JagdtigerAusfb/Rubiks_Cube_Solving_Robot_EXTENCUBE_UNICAMP/1. RAIDEN/3D Files/Cap_garra_v3.png

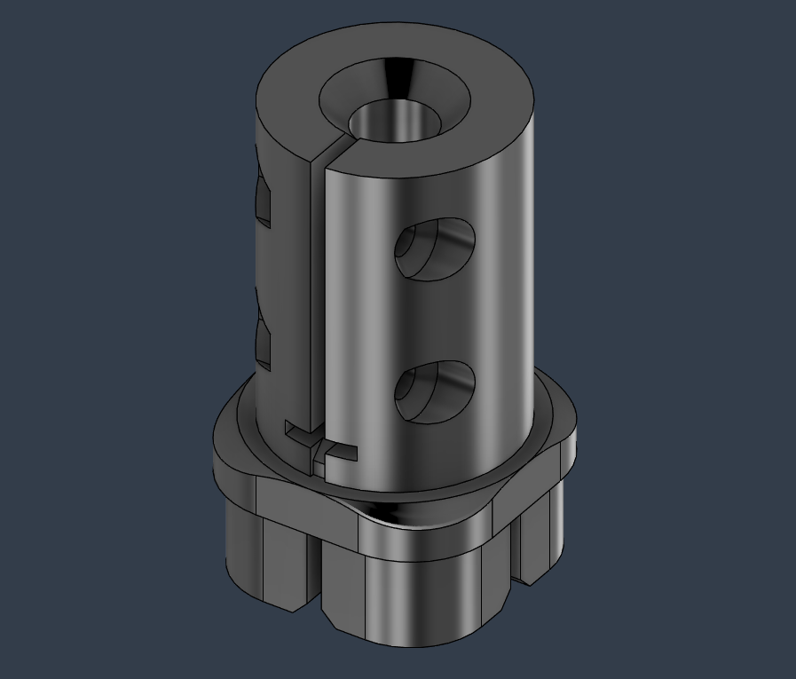
1. RAIDEN/3D Files/Cap_garra_v3.png
