JagdtigerAusfb/Rubiks_Cube_Solving_Robot_EXTENCUBE_UNICAMP/1. RAIDEN/3D Files/Gabarito_Final.png

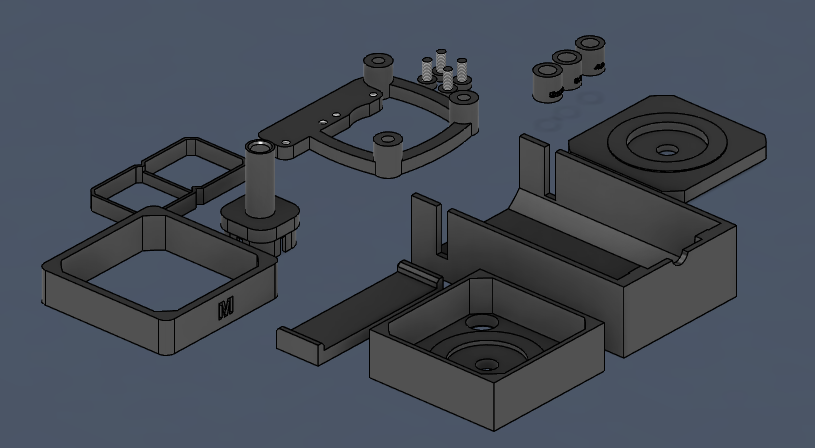
1. RAIDEN/3D Files/Gabarito_Final.png
