JagdtigerAusfb/Rubiks_Cube_Solving_Robot_EXTENCUBE_UNICAMP/1. RAIDEN/PCB/PCB 3 Drivers/3DriversA4988.png

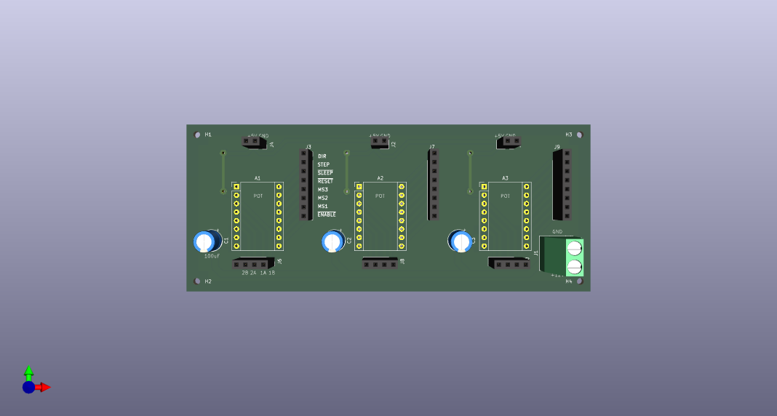
1. RAIDEN/PCB/PCB 3 Drivers/3DriversA4988.png
