JagdtigerAusfb/Rubiks_Cube_Solving_Robot_EXTENCUBE_UNICAMP/1. RAIDEN/PCB/PCB Drivers + Sensores/PCB Drivers + Sensores/PCB Drivers + Sensores.png

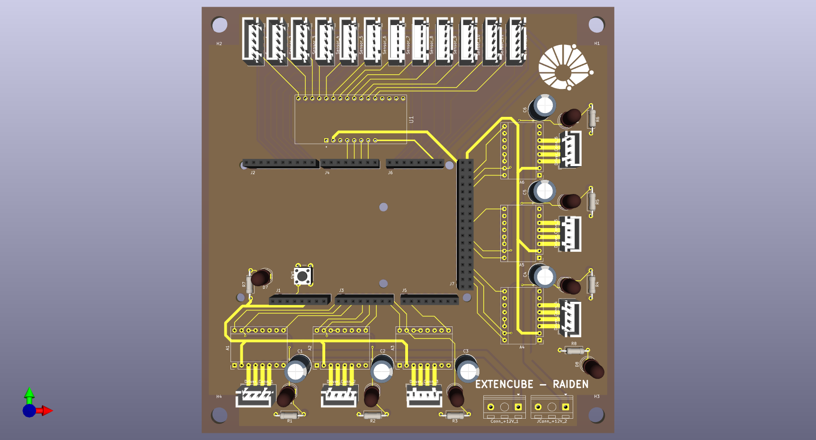
1. RAIDEN/PCB/PCB Drivers + Sensores/PCB Drivers + Sensores/PCB Drivers + Sensores.png
