JagdtigerAusfb/Rubiks_Cube_Solving_Robot_EXTENCUBE_UNICAMP/3. Códigos de Teste ou Demonstração/Sensores/Códigos Gerais/BETA/Calibração_V3_BETA.docx

#include <Wire.h>

#include <string.h>

/* Estrutura da Calibração

Esse código implementa a estrutura do

fluxograma da Calibração Completa do

Sistema dos Sensores.

*/

void ini_calib() {

// Inicializa Variáveis

int face, position, estado = 0, 0, 0;

int progression[6] = {0};

float calibration[12][6] = {-1};

// Define Constantes de Operação do Sistema

//Inserir aqui Parametros peso de HSV

int ordem[6][6] = {

{0, 1, 3, 4, 5, 2},

{1, 5, 4, 2, 0, 3},

{2, 1, 5, 4, 0, 3},

{3, 1, 0, 4, 2, 5},

{4, 2, 1, 5, 3, 0},

{5, 4, 2, 1, 3, 0}

};

int seq_faces[] = {

0,3, 0,3, 0,3, 0,3,

2,1,5,4, 2,1,5,4, 2,1,5,4, 2,1,5,4,

0,3, 0,3,

2,5, 2,5,

1,4, 1,4

};

char seq_moves[][7] = {

"PG", "PG", "PG", "PG",

"A", "A", "A",

"AEBK", "JAFBK",

"JAFHP", "GQFHP",

"GQEQEM", "DNREM",

"DNQ"

};

bool flags_move[] = {

0,0,1,0,1,0,1,0,

1,0,0,0, 1,0,0,0, 1,0,0,0, 1,0,0,0,

1,0,1,0,

1,0,1,0,

1,0,1,0,

1

};

}

void setup() {

Serial.begin(115200);

Wire.begin();

ini_calib();

}

void sens_calib() {

int NS = 2*face + position;

// Ler RGB Sensor NS (precisa acionar portas especificas, fazer com switch case)

// Converter RGB para HSV

float H_medido = 0.0; //exemplo

int b = progression[face];

int indice = ordem[face][b];

calibration[NS][indice] = H_medido;

estado++;

}

void loop_calibration() {

while(1) {

sens_calib();

if (position == 0){

position = 1;

continue;

}

position = 0;

progression[face]++;

if (estado == 72) {

//Faz Etapas Finais para encerrrar Calibração

break;

}

int a = estado>>1;

face = seq_faces[a];

if (flags_move[a]) {

char move[7];

strcpy(move, seq_moves[a]);

// Executar move da string pega acima

}

}

}

void loop() {

loop_calibration();

}
