JagdtigerAusfb/Rubiks_Cube_Solving_Robot_EXTENCUBE_UNICAMP/3. Códigos de Teste ou Demonstração/Sensores/Códigos Gerais/BETA/Calibração_V4_BETA_MONOBLOCO.docx

#include <Wire.h>

#include <string.h>

#include "TCS34725.h"

/* Estrutura da Calibração

Esse código implementa a estrutura do

fluxograma da Calibração Completa do

Sistema dos Sensores.

*/

TCS34725 tcs;

#define AMOSTRAS 20

int NS;

bool ini_calib;

// MULTIPLEXADOR

#define LED_0 0

#define LED_1 1

#define LED_2 2

#define LED_3 3

#define LED_4 4

#define LED_5 5

#define LED_6 6

#define LED_7 7

#define LED_8 8

#define LED_9 9

#define LED_10 10

#define LED_11 11

#define EN_MUX 18

#define MUX_0 17

#define MUX_1 16

#define MUX_2 15

#define MUX_3 14

//

//PARTE DOS MOTORES

#define DIR_PIN_1 31

#define STEP_PIN_1 30

#define DIR_PIN_2 35

#define STEP_PIN_2 34

#define DIR_PIN_3 A12

#define STEP_PIN_3 A13

#define DIR_PIN_4 A6

#define STEP_PIN_4 A7

#define DIR_PIN_5 A0

#define STEP_PIN_5 A1

#define DIR_PIN_6 43

#define STEP_PIN_6 42

#define ENABLE_PIN_1 14

#define ENABLE_PIN_2 16

#define ENABLE_PIN_3 49

#define ENABLE_PIN_4 48

#define ENABLE_PIN_5 A3

#define ENABLE_PIN_6 19

// ================================

// CONFIG

// ================================

#define MAX_SEQ 350

char lineBuffer[50];

char sequencia[MAX_SEQ];

int seqLen = 0;

int DELAY_STEP = 1000;

int DELAY_ENTRE_MOV = 10;

bool recebendo = false;

// ================================

// CONFIGURAR MOTOR

// ================================

bool configurarMotor(char m, int &dirPin, int &stepPin, int &enablePin, int &dir, int &passos) {

switch(m) {

case 'A': dirPin=DIR_PIN_1; stepPin=STEP_PIN_1; enablePin=ENABLE_PIN_1; dir=LOW; passos=50; break;

case 'B': dirPin=DIR_PIN_1; stepPin=STEP_PIN_1; enablePin=ENABLE_PIN_1; dir=HIGH; passos=50; break;

case 'C': dirPin=DIR_PIN_1; stepPin=STEP_PIN_1; enablePin=ENABLE_PIN_1; dir=LOW; passos=100; break;

case 'D': dirPin=DIR_PIN_2; stepPin=STEP_PIN_2; enablePin=ENABLE_PIN_2; dir=LOW; passos=50; break;

case 'E': dirPin=DIR_PIN_2; stepPin=STEP_PIN_2; enablePin=ENABLE_PIN_2; dir=HIGH; passos=50; break;

case 'F': dirPin=DIR_PIN_2; stepPin=STEP_PIN_2; enablePin=ENABLE_PIN_2; dir=LOW; passos=100; break;

case 'G': dirPin=DIR_PIN_3; stepPin=STEP_PIN_3; enablePin=ENABLE_PIN_3; dir=LOW; passos=50; break;

case 'H': dirPin=DIR_PIN_3; stepPin=STEP_PIN_3; enablePin=ENABLE_PIN_3; dir=HIGH; passos=50; break;

case 'I': dirPin=DIR_PIN_3; stepPin=STEP_PIN_3; enablePin=ENABLE_PIN_3; dir=LOW; passos=100; break;

case 'J': dirPin=DIR_PIN_4; stepPin=STEP_PIN_4; enablePin=ENABLE_PIN_4; dir=LOW; passos=50; break;

case 'K': dirPin=DIR_PIN_4; stepPin=STEP_PIN_4; enablePin=ENABLE_PIN_4; dir=HIGH; passos=50; break;

case 'L': dirPin=DIR_PIN_4; stepPin=STEP_PIN_4; enablePin=ENABLE_PIN_4; dir=LOW; passos=100; break;

case 'M': dirPin=DIR_PIN_5; stepPin=STEP_PIN_5; enablePin=ENABLE_PIN_5; dir=LOW; passos=50; break;

case 'N': dirPin=DIR_PIN_5; stepPin=STEP_PIN_5; enablePin=ENABLE_PIN_5; dir=HIGH; passos=50; break;

case 'O': dirPin=DIR_PIN_5; stepPin=STEP_PIN_5; enablePin=ENABLE_PIN_5; dir=LOW; passos=100; break;

case 'P': dirPin=DIR_PIN_6; stepPin=STEP_PIN_6; enablePin=ENABLE_PIN_6; dir=LOW; passos=50; break;

case 'Q': dirPin=DIR_PIN_6; stepPin=STEP_PIN_6; enablePin=ENABLE_PIN_6; dir=HIGH; passos=50; break;

case 'R': dirPin=DIR_PIN_6; stepPin=STEP_PIN_6; enablePin=ENABLE_PIN_6; dir=LOW; passos=100; break;

default: return false;

}

return true;

}

// ================================

// EXECUÇÕES

// ================================

void executarSimples(char m){

int d,s,e,dir,p;

if(!configurarMotor(m,d,s,e,dir,p)) return;

digitalWrite(e,LOW);

digitalWrite(d,dir);

for(int i=0;i<p;i++){

digitalWrite(s,HIGH);

delayMicroseconds(DELAY_STEP);

digitalWrite(s,LOW);

delayMicroseconds(DELAY_STEP);

}

digitalWrite(e,HIGH);

delay(DELAY_ENTRE_MOV);

}

//

void setup() {

Serial.begin(115200);

Wire.begin();

tcs.integrationTime(33);

tcs.gain(TCS34725::Gain::X01);

ini_calib = true;

//Sensor

pinMode(LED_0, OUTPUT);

pinMode(LED_1, OUTPUT);

pinMode(LED_2, OUTPUT);

pinMode(LED_3, OUTPUT);

pinMode(LED_4, OUTPUT);

pinMode(LED_5, OUTPUT);

pinMode(LED_6, OUTPUT);

pinMode(LED_7, OUTPUT);

pinMode(LED_8, OUTPUT);

pinMode(LED_9, OUTPUT);

pinMode(LED_10, OUTPUT);

pinMode(LED_11, OUTPUT);

pinMode(EN_MUX, OUTPUT);

pinMode(MUX_0, OUTPUT);

pinMode(MUX_1, OUTPUT);

pinMode(MUX_2, OUTPUT);

pinMode(MUX_3, OUTPUT);

//Motor

pinMode(ENABLE_PIN_1,OUTPUT); digitalWrite(ENABLE_PIN_1,HIGH);

pinMode(ENABLE_PIN_2,OUTPUT); digitalWrite(ENABLE_PIN_2,HIGH);

pinMode(ENABLE_PIN_3,OUTPUT); digitalWrite(ENABLE_PIN_3,HIGH);

pinMode(ENABLE_PIN_4,OUTPUT); digitalWrite(ENABLE_PIN_4,HIGH);

pinMode(ENABLE_PIN_5,OUTPUT); digitalWrite(ENABLE_PIN_5,HIGH);

pinMode(ENABLE_PIN_6,OUTPUT); digitalWrite(ENABLE_PIN_6,HIGH);

pinMode(DIR_PIN_1,OUTPUT); pinMode(STEP_PIN_1,OUTPUT);

pinMode(DIR_PIN_2,OUTPUT); pinMode(STEP_PIN_2,OUTPUT);

pinMode(DIR_PIN_3,OUTPUT); pinMode(STEP_PIN_3,OUTPUT);

pinMode(DIR_PIN_4,OUTPUT); pinMode(STEP_PIN_4,OUTPUT);

pinMode(DIR_PIN_5,OUTPUT); pinMode(STEP_PIN_5,OUTPUT);

pinMode(DIR_PIN_6,OUTPUT); pinMode(STEP_PIN_6,OUTPUT);

}

void rgbToHsv(float r, float g, float b, float &h, float &s, float &v) {

float maxc = max(r, max(g, b));

float minc = min(r, min(g, b));

float delta = maxc - minc;

v = maxc;

if (maxc == 0) { s = 0; h = 0; return; }

s = delta / maxc;

if (delta == 0) h = 0;

else if (maxc == r) h = 60.0 * fmod(((g - b) / delta), 6);

else if (maxc == g) h = 60.0 * (((b - r) / delta) + 2);

else h = 60.0 * (((r - g) / delta) + 4);

if (h < 0) h += 360.0;

}

float sensor() {

if (!tcs.attach(Wire)) {

Serial.print("Sensor ");

Serial.print(NS);

Serial.println(" nao encontrado!");

// Aguarda Sensor conectar

while (1);

}

delay(4000); // alterar delay?

int validas = 0;

float H_mean = -1;

float somaHue = 0;

for (int i = 0; i < AMOSTRAS; i++) {

while (!tcs.available());

auto c = tcs.color();

float r = c.r, g = c.g, b = c.b;

float soma = r + g + b;

if (soma < 5) continue;

r /= soma;

g /= soma;

b /= soma;

float h, s, v;

rgbToHsv(r, g, b, h, s, v);

somaHue += h;

validas++;

if (validas > 0) {H_mean = somaHue / validas;}

delay(50);

return(H_mean);

}

}

void MUX(int n){

digitalWrite(EN_MUX, LOW);

digitalWrite(LED_0, LOW);

digitalWrite(LED_1, LOW);

digitalWrite(LED_2, LOW);

digitalWrite(LED_3, LOW);

digitalWrite(LED_4, LOW);

digitalWrite(LED_5, LOW);

digitalWrite(LED_6, LOW);

digitalWrite(LED_7, LOW);

digitalWrite(LED_8, LOW);

digitalWrite(LED_9, LOW);

digitalWrite(LED_10, LOW);

digitalWrite(LED_11, LOW);

switch(n) {

case 1:

digitalWrite(LED_1, HIGH);

break;

case 2:

digitalWrite(LED_2, HIGH);

break;

case 3:

digitalWrite(LED_3, HIGH);

break;

case 4:

digitalWrite(LED_4, HIGH);

break;

case 5:

digitalWrite(LED_5, HIGH);

break;

case 6:

digitalWrite(LED_6, HIGH);

break;

case 7:

digitalWrite(LED_7, HIGH);

break;

case 8:

digitalWrite(LED_8, HIGH);

break;

case 9:

digitalWrite(LED_9, HIGH);

break;

case 10:

digitalWrite(LED_10, HIGH);

break;

case 11:

digitalWrite(LED_11, HIGH);

break;

default:

digitalWrite(LED_0, HIGH);

} // Liga o LED do sensor NS

if (NS & 1<<0) {digitalWrite(MUX_0, HIGH);}

else{digitalWrite(MUX_0, LOW);}

if (NS & 1<<1) {digitalWrite(MUX_1, HIGH);}

else{digitalWrite(MUX_1, LOW);}

if (NS & 1<<2) {digitalWrite(MUX_2, HIGH);}

else{digitalWrite(MUX_2, LOW);}

if (NS & 1<<3) {digitalWrite(MUX_3, HIGH);}

else{digitalWrite(MUX_3, LOW);}

//Seleciona Sensor NS pelo MUX

digitalWrite(EN_MUX, HIGH); // Habilita MUX

}

void imprimirCalib(float matriz[][6], int linhas, int colunas) {

Serial.println();

Serial.println("============= CALIBRATION =============");

String nomesColunas[6] = {"White", "Red", "Green", "Yellow", "Orange", "Blue"};

String nomesLinhas[12] = {"Ue", "Uc", "Re", "Rc", "Fe", "Fc", "De", "Dc", "Le", "Lc", "Be", "Bc"};

// Cabeçalho

Serial.print("\t");

for (int j = 0; j < colunas; j++) {

Serial.print(nomesColunas[j]);

Serial.print("\t");

}

Serial.println();

// Linhas da matriz

for (int i = 0; i < linhas; i++) {

Serial.print(nomesLinhas[i]);

Serial.print("\t");

for (int j = 0; j < colunas; j++) {

Serial.print(matriz[i][j], 2); // 2 casas decimais

Serial.print("\t");

}

Serial.println();

}

}

void calibration() {

if (ini_calib) { // Inicialização Parâmetros

ini_calib = false;

bool end_calib = false;

//void ini_calib(){ Inicializa Variáveis

int face = 0;

int position = 0;

int estado = 0;

int progression[6] = {0};

float calib[12][6] = {-1};

// Define Constantes de Operação do Sistema

//Inserir aqui Parametros peso de HSV

int ordem[6][6] = {

{0, 1, 3, 4, 5, 2},

{1, 5, 4, 2, 0, 3},

{2, 1, 5, 4, 0, 3},

{3, 1, 0, 4, 2, 5},

{4, 2, 1, 5, 3, 0},

{5, 4, 2, 1, 3, 0}

};

int seq_faces[] = {

0,3, 0,3, 0,3, 0,3,

2,1,5,4, 2,1,5,4, 2,1,5,4, 2,1,5,4,

0,3, 0,3,

2,5, 2,5,

1,4, 1,4

};

char seq_moves[][7] = {

"PG", "PG", "PG", "PG",

"A", "A", "A",

"AEBK", "JAFBK",

"JAFHP", "GQFHP",

"GQEQEM", "DNREM",

"DNQ"

};

bool flags_move[] = {

0,0,1,0,1,0,1,0,

1,0,0,0, 1,0,0,0, 1,0,0,0, 1,0,0,0,

1,0,1,0,

1,0,1,0,

1,0,1,0,

1

};

//}

}

while(~end_calib) {

//void sens_calib() {

int NS = 2*face + position;

MUX(NS);

//Sensoria

float H = sensor();

if (H>0){

int b = progression[face];

int indice = ordem[face][b];

calib[NS][indice] = H;

}

estado++;

//}

if (position == 0){

position = 1;

continue;

}

position = 0;

progression[face]++;

if (estado == 72) {

//Imprime matriz calibração

imprimirCalib(calib, 12, 6);

end_calib = true;

break;

}

int a = estado>>1;

face = seq_faces[a];

if (flags_move[a]) {

char move[7];

strcpy(move, seq_moves[a]);

int j = 0;

while (move[j]!='\0') {

executarSimples(move[j]);

// Executa move do caractere acima

j++;

}

continue;

}

}

}

void loop() {

calibration();

}
