JagdtigerAusfb/Rubiks_Cube_Solving_Robot_EXTENCUBE_UNICAMP/3. Códigos de Teste ou Demonstração/Sensores/Códigos Gerais/BETA/Leitura_Embaralhamento_V1_BETA.docx

#include <Wire.h>

/* Estrutura da Leitura Embaralhamento

Esse código implementa a estrutura do

fluxograma da Leitura Embaralhamento do

Sistema dos Sensores.

*/

void ini_shuf() {

// Inicializa Variáveis

int face, position, estado = 0, 0, 0;

int progression[6] = {0};

char shuffle[6][8];

// Define Constantes de Operação do Sistema

//Inserir aqui Parametros peso de HSV

int seq_faces[] = {

0,3, 0,3, 0,3, 0,3,

2,5, 2,5, 2,5, 2,5,

1,4, 1,4, 1,4, 1,4

};

const char* seq_moves[] = {

"BK", "BK", "BK", "BK",

"HQ", "HQ", "HQ", "HQ",

"EN", "EN", "EN", "EN"

};

bool flags_move[] = {

0,0, 1,0, 1,0, 1,0,

1,0, 1,0, 1,0, 1,0,

1,0, 1,0, 1,0, 1,0,

1

};

float calib[12][6];

//Integrar com o código de calibração

}

void setup() {

Serial.begin(115200);

Wire.begin();

ini_shuf();

}

void sens_shuf() {

int NS = 2*face + position;

// Ler RGB Sensor NS (precisa acionar portas especificas, fazer com switch case)

// Converter RGB para HSV

float H_medido = 0.0; //exemplo

for(i<=6) {

float H_Ref = calib[NS][i]

// Calcula distancias e trata dados

}

// Classifica o valor associando a um char (cor)

char cor = 'G'; // Exemplo.

int indice = progression[face];

shuffle[face][indice] = cor;

estado++;

progression[face]++

}

void loop_shuffle() {

while(1){

sens_shuf();

if (position == 0){

position = 1;

continue;

}

position = 0;

if (estado == 48) {

// Faz etapas finais de leitura de embaralhamento

break;

}

int a = estado>>1;

face = seq_faces[a];

if (flags_move[a]) {

const char* move = seq_moves[a];

// Executar move da string pega acima

}

}

}

void loop() {

loop_shuffle();

}
