JagdtigerAusfb/Rubiks_Cube_Solving_Robot_EXTENCUBE_UNICAMP/1. RAIDEN/Software/Cube App Sensores/firmware/src/sensing/sensing.h

#ifndef SENSING_H
#define SENSING_H
#include <Arduino.h>
#include <Wire.h>
#include "TCS34725.h"                 // lib única (hideakitai)

#define NUM_SENSORS   12
#define NUM_COLORS    6

// Pinos de seleção do mux 74HC4067 (S0..S3). TODO(hw): confirmar.
#define MUX_SEL_0 11
#define MUX_SEL_1 10
#define MUX_SEL_2 9
#define MUX_SEL_3 8

#define LED_PIN         7             // liga/desliga o conjunto de LEDs (sem seleção individual)
#define SENSE_SETTLE_MS 60            // acomodação após trocar canal (~1 integração)

// Indireção NS lógico (2*face+pos, ordem de contrato) -> canal físico do mux.
extern const uint8_t MUX_CHANNEL[NUM_SENSORS];
// Char de cor por índice (ordem de contrato por face): 0=W 1=R 2=G 3=Y 4=O 5=B.
extern const char COLOR_CHAR[NUM_COLORS];

struct Hsv { float h, s, v; };

extern TCS34725 tcs;                  // instância única (definida em scan.cpp)

// Referência GLOBAL de cor (aplicada a todos os sensores) e matriz de estado.
extern Hsv  globalRef[NUM_COLORS];    // definidos em detect_color.cpp
extern float whiteBal[3]; // resposta do sensor ao branco (von Kries)
extern float whiteSatThresh; // fronteira de saturação branco<->cromáticos
extern char scramble[6][8];
extern const char    FACE_TURN[6];       // N' de cada face (ordem U,R,F,D,L,B)
extern const uint8_t POS[6][2][4];       // [face][papel:0=quina,1=centro][passo] -> índice 0..7


// ---- Fundação ----
void    sensingInit();
void    muxSelect(uint8_t physicalChannel);
uint8_t sensingScan(bool status[NUM_SENSORS]);

// ---- Driver de cor ----
void detectColorLoadDefaults();               // placeholder de globalRef (pré-calibração)
bool senseHsv(uint8_t ns, Hsv &out);          // leitura crua: mux+read+rgb->hsv; false se inválida
char detectColorLogical(uint8_t ns);          // senseHsv + classificação -> W/R/G/Y/O/B/X
bool senseRaw(uint8_t ns, float &r, float &g, float &b);   // leitura CRUA (sem balanço)

// ---- Calibração ----
int calibrateSolved();                       // 12 leituras (cubo resolvido) -> globalRef

// ---- Sensoriamento ----
int senseComplete();

#endif // SENSING_H
